Alparrrr/ZASS_MANTIS/04_DWIN_DISPLAY/32/4.jpg

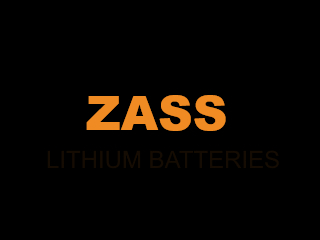
04_DWIN_DISPLAY/32/4.jpg
