Alparrrr/ZASS_MANTIS/02_Firmware_STM32/ZASS_MANTIS_114/Core/Inc/main.h

#define SD_SPI_HANDLE hspi1
#define SPI1_CS_Pin GPIO_PIN_4
#define SPI1_CS_GPIO_Port GPIOA
