Alparrrr/ZASS_MANTIS/02_Firmware_STM32/ZASS_MANTIS_114/Core/Inc/Task_SDCard.h

/*
 * Task_SDCard.h
 *
 *  Created on: Feb 10, 2026
 *      Author: ALPER
 */

#ifndef INC_TASK_SDCARD_H_
#define INC_TASK_SDCARD_H_

void SD_Hardware_Wakeup(void);
void SD_Log_Process(void);
#endif /* INC_TASK_SDCARD_H_ */
